agkaminski/Pocket265/fw/dl1414.c

/* Pocket265 DL1414T LED display driver
 * A.K. 2022
 */

#include <pocket265.h>
#include <ctype.h>
#include <string.h>

#include "dl1414.h"

void dl1414_puts(const char *str)
{
	static int pos = 0;
	volatile unsigned char *ptr = (void *)SCREEN_BASE;
	static char buff[SCREEN_LENGTH];
	char i, j, c;

	for (i = 0; str[i] != '\0'; ++i) {
		if (str[i] == '\n' || str[i] == '\r') {
			pos = 0;

			if (str[i] == '\n')
				memset(buff, 0, sizeof(buff));

			continue;
		}

		c = str[i];

		if (isalpha(c))
			c = toupper(c);

		if (pos >= SCREEN_LENGTH) {
			for (j = 1; j < SCREEN_LENGTH; ++j)
				buff[j - 1] = buff[j];

			buff[SCREEN_LENGTH - 1] = c;
		}
		else {
			buff[pos++] = c;
		}
	}

	for (i = 0; i < sizeof(buff); ++i)
		ptr[SCREEN_LENGTH - 1 - i] = buff[i];
}
