agkaminski/Pocket265/user/cc65/simak65/addrmode.h

/* SimAK65 addresing mode
 * Copyright A.K. 2018, 2023
 */

#ifndef SIMAK65_ADDRMODE_H_
#define SIMAK65_ADDRMODE_H_

#include "types.h"
#include "decoder.h"
#include "simak65.h"

enum argtype { arg_none, arg_byte, arg_addr };

u8 addrmode_nextpc(struct simak65_cpustate *cpu);

enum argtype addrmode_getArgs(struct simak65_cpustate *cpu, u8 *args, enum addrmode mode, unsigned int *cycles);

#endif /* SIMAK65_ADDRMODE_H_ */
