agkaminski/Pocket265/user/cc65/simak65/flags.h

/* SimAK65 CPU flags
 * Copyright A.K. 2018, 2023
 */

#ifndef SIMAK65_FLAGS_H_
#define SIMAK65_FLAGS_H_

#define FLAG_CARRY 0x01
#define FLAG_ZERO  0x02
#define FLAG_IRQD  0x04
#define FLAG_BCD   0x08
#define FLAG_BRK   0x10
#define FLAG_ONE   0x20
#define FLAG_OVRF  0x40
#define FLAG_SIGN  0x80

#endif /* SIMAK65_FLAGS_H_ */
