agkaminski/Pocket265/user/cc65/simak65/types.h

/* SimAK65 internal types
 * Copyright A.K. 2018, 2023
 */

#ifndef SIMAK65_TYPES_H_
#define SIMAK65_TYPES_H_

#include <stdint.h>

typedef uint8_t  u8;
typedef uint16_t u16;
typedef uint32_t u32;

typedef int8_t   s8;
typedef int16_t  s16;
typedef int32_t  s32;

#endif /* SIMAK65_TYPES_H_ */
